Chrismettal/ESP-Hiro/img/Nice2.png

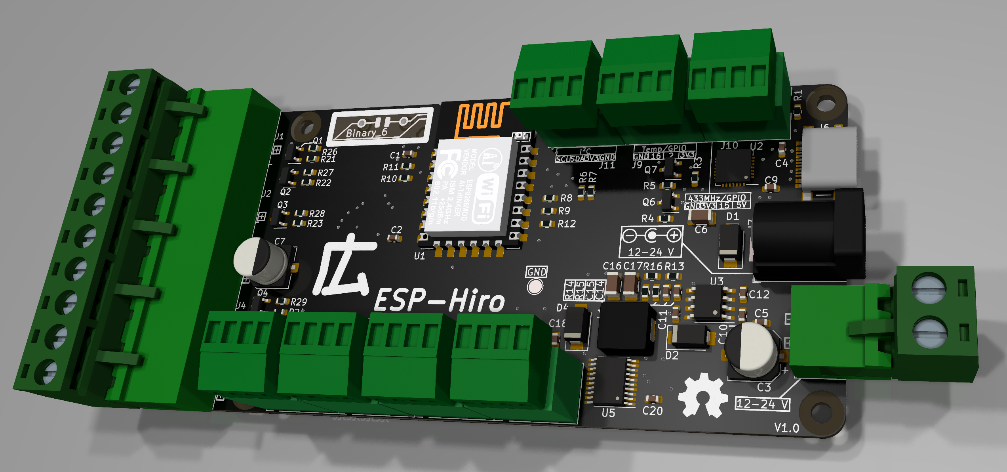
img/Nice2.png
